RoboticsBrno/semafor/fw/semafor_basic/src/semafor.cpp

#include "Arduino.h"
#include "stateVector.h"
#include "semafor.h"
#include <ctype.h>

#define SECOND 1000
#define MINUTE SECOND*60

String wifi_ssid = "Semafor";
String wifi_password = "adminadmin";
IPAddress wifiIP(192, 168, 1, 1);
IPAddress wifiIPtest(192, 168, 1, 100);
IPAddress netMsk(255, 255, 255, 0);

DNSServer dnsServer;
ESP8266WebServer server(80);

StateVector stateVector;
uint8_t semaforID = 0;

// semafor game config
EEPROM_data stateVector_eeprom(&stateVector, sizeof(stateVector));

// semafor ID
EEPROM_data semaforID_eeprom(&semaforID, sizeof(semaforID));

// UDP server for sharing settings between semafors
WiFiUDP udpSett;
uint8_t udpCheckKey;

uint8_t prevMode = 0;
uint8_t DNS_PORT = 53;


// bool activeLed = false;

void setLed(uint8_t ledID, bool on) {
    if(stateVector.activeLed) {
        analogWrite(ledPins[ledID], on*stateVector.ledBrightness[0]*4);
    }
}
void setLeds(bool red, bool green, bool blue) {
    setLed(0, red);
    setLed(1, green);
    setLed(2, blue);
}
void setLedsAll(bool state) {
    setLed(0, state);
    setLed(1, state);
    setLed(2, state);
}

bool buttonPressed(uint16_t timeMs, bool activeEnd = 1) {
    static uint32_t lastPressed = 0;

    if(activeEnd) {
        if(digitalRead(button)) {
            // not pressed
            lastPressed = 0;
        }
        else if(lastPressed == 0) {
            // firstly pressed
            lastPressed = millis();
        }
        else if(millis() > (lastPressed + timeMs)) {
            // still pressed after time period
            lastPressed = 0;
            return true;
        }
    }
    else {
        if(!digitalRead(button) && millis() > (lastPressed + timeMs)) {
            lastPressed = millis();
            return true;
        }
    }

    return false;
}

void printInfo(semState state) {
    Serial.printf("semaforID: %d\n", semaforID);
    Serial.printf("semafor state: %d\n", state);
    Serial.printf("gameMode: %d\n", stateVector.gameMode);
    Serial.printf("monopolyDelayMin: %d\n", stateVector.monopolyDelayMin);
    Serial.printf("monopolyDelayMax: %d\n", stateVector.monopolyDelayMax);
    Serial.printf("tdPressShort: %d\n", stateVector.tdPressShort);
    Serial.printf("tdPressLong: %d\n", stateVector.tdPressLong);
    Serial.printf("\n");
}

void initLeds() {
    stateVector.activeLed = true;
    for(uint8_t i = 0; i < 3; ++i) {
        pinMode(ledPins[i], OUTPUT);
    }
}

void initSerial() {
    stateVector.activeLed = false;
    Serial.begin(115200);
    for(uint8_t i = 0; i < 3; ++i) {
        pinMode(ledPins[i], SPECIAL);
    }
}


void semaforInit() {
    stateVector_eeprom.read();
    semaforID_eeprom.read();

    initLeds();
    // initSerial();


    pinMode(button, INPUT_PULLUP);

    randomSeed(analogRead(A0));

    delay(500);

    for(int i = 0; i< 3; i++) {
        setLed(i, true);
        delay(200);
    }

    for(int i = 2; i>=0; i--) {
        setLed(i, false);
        delay(200);
    }
}

void settBrodcast() {
    static bool initBrodcast = true;
    static bool blinkCenter = true;
    static ArduinoMetronome blinker(800);
    static ArduinoMetronome sender(500);

    if(initBrodcast) {
        setLeds(true, false, true);

        Serial.println("Start WiFi");
        softApEnable();

        // server routes
        server.on("/", handleRoot);
        server.on("/admin", handleAdmin);
        server.on("/adminsave", handleAdminSave);
        server.on("/datasave", handleDataSave);
        server.on("/addparam", handleAddParam);
            // put "IP/addparam?id=X" into URL for setting semafor ID
            // put "IP/addparam?led=1/0" enable LED / enable Serial
        server.onNotFound(handleRoot);
        server.on("/style.css", handleStyle);
        server.begin();


        // UDP server for sharing settings between semafors
        udpSett.begin(1111);
        initBrodcast = false;
    }

    if(blinker.loopMs()) {
        if(blinkCenter) {
            setLeds(false, true, false);
        }
        else {
            setLeds(true, false, true);
        }
        blinkCenter = !blinkCenter;
    }

    if(sender.loopMs()) {
        Serial.println("Clients coutn: " + String(wifi_softap_get_station_num()));
        struct station_info *station_list = wifi_softap_get_station_info();
        while (station_list != NULL) {
            IPAddress station_ip = ((&station_list->ip)->addr);

            // Serial.println(station_ip.toString());
            udpSett.beginPacket(station_ip, 1111);
            stateVector.transmittCheckNum = semaforID;
            udpSett.write((const uint8_t *) &stateVector, sizeof(stateVector));
            udpSett.endPacket();

            station_list = STAILQ_NEXT(station_list, next);
        }
        wifi_softap_free_station_info();
    }
}

bool settReceive() {
    static bool initReceive = true;
    static bool initConnected = true;
    static bool connected = false;

    static ArduinoMetronome sender(800);

    if(initReceive) {
        wifiEnableConnect();
        initReceive = false;
    }

    if(initConnected && WiFi.status() == WL_CONNECTED) {
        initConnected = false;
        connected = true;
        udpSett.begin(1111);
        Serial.println("Connected to WiFi");
    }

    if(connected) {
        StateVector receiveVector;

        int packetSize = udpSett.parsePacket();
        if (packetSize) {
            int len = udpSett.read((char *) &receiveVector, sizeof(receiveVector));
            if(len>0) {
                stateVector = receiveVector;
                stateVector_eeprom.write();
                Serial.printf("New settings recieved and updated from Semafor ID: %d", receiveVector.transmittCheckNum);

                // success upload blink
                for(int i = 0; i < 6; i++) {
                    setLeds(false, true, true);
                    delay(80);
                    setLeds(true, true, false);
                    delay(80);
                }
                setLeds(false, false, false);
                wifiDisable();

                return true; // jump to Normal mode
            }
            else {
                Serial.printf("Error receive new settings from Semafor ID: %d", receiveVector.transmittCheckNum);
            }
        }
    }

    return false;



}


semState semaforState() {

    semState nowState = S_RECEIVE;

    static bool pressedOnStart = false;
    static int startPressedTime;
    static int startTime = millis();
    int nowTime = millis();

    if(nowTime-startTime < 2 * MINUTE) {
        bool buttonState = !digitalRead(button);

        if(!buttonState) {
            pressedOnStart = false;
            nowState = S_RECEIVE; // if not pressed + until specific time
        }
        else if(buttonState && pressedOnStart == false) { // first press
            startPressedTime = millis();
            pressedOnStart = true;
            nowState = S_RECEIVE;
        }
        else if(pressedOnStart && nowTime-startPressedTime > 3 * SECOND) {
            nowState = S_BRODCAST; //if pressed for 3 sec + until specific time
        }
    }
    else {
        nowState = S_NORMAL; // else
        WiFi.disconnect(true);
    }

    return nowState;
}


void semaforLoop() {
    switch(stateVector.gameMode) {
        case 0:
            handleMonopoly();
            break;
        case 1:
            handleVabicka();
            break;
        case 2:
            handleVlajky();
            break;
        case 3:
            handleTowerDefence();
            break;
        case 4:
            handleHoldToGet();
            break;
        case 5:
            handleMinutka();
            break;
        case 6:
            handleMikrovlnka();
            break;
        default:
            stateVector.gameMode = 0;
    }
    prevMode = stateVector.gameMode;
}


void handleMonopoly() {
    static uint32_t changeDelay = 0;
    static uint32_t lastChange = 0;
    static bool lightStateRG = 1; //0-red, 1-green
    if(stateVector.gameMode != prevMode) {
        lightStateRG = 0;
        lastChange = millis();
    }
    if(millis() > (lastChange + changeDelay)) {
        lastChange = millis();
        changeDelay = 1000 * random(stateVector.monopolyDelayMin, stateVector.monopolyDelayMax);

        lightStateRG = !lightStateRG;
    }
    setLeds(!lightStateRG, lightStateRG, 0);
}
void handleVabicka() {
    static int8_t lightState = 0;  //0-R, 1-G, 2-B, 3-nothing
    if(stateVector.gameMode != prevMode)
        lightState = 0;
    if(buttonPressed(debounce, 0)) {
        ++lightState;
        if(lightState > 2)
            lightState = 0;
    }
    for(uint8_t i = 0; i < 3; ++i) {
        setLed(i, i == lightState);
    }
}
void handleVlajky() {
    static int8_t lightState = 0;  //0-R, 1-G, 2-B, 3-nothing
    if(stateVector.gameMode != prevMode)
        lightState = 0;
    if(buttonPressed(debounce, 0)) {
        ++lightState;
        if(lightState > 3)
            lightState = 0;
    }
    for(uint8_t i = 0; i < 3; ++i) {
        setLed(i, i == lightState);
    }
}
void handleTowerDefence() {
    static uint32_t lastPress = 0;
    static int8_t lightState = 0;  //0-R, 1-G, 2-B, 3-nothing
    static uint8_t buildState = 0; //0-building, 1-short flashing, 2-destroying, 3-flashing
    static bool prevButtonState = 0, buttonState = 0;
    static uint32_t buttonPressedSince = 0;
    if(stateVector.gameMode != prevMode) {
        buildState = 0;
        lightState = 0;
    }
    switch(buildState) {
        case 0:     //building
            buttonState = digitalRead(button);
            if((buttonState && !prevButtonState) && millis() > (lastPress + debounce)) {
                lastPress = millis();
                ++lightState;   //0-nothing, 1-R, 2-RG, 3-RGB
                if(lightState > 3)
                    lightState = 3;
            }
            prevButtonState = buttonState;
            break;
        case 1:     //short flashing
            static uint32_t flashStart = 0;
            static uint8_t flashesCount = 0;
            static int8_t tempLightState;
            if(flashesCount == 0)
                tempLightState = lightState;
            if(millis() > (flashStart + flashPeriod)) {
                flashStart = millis();
                ++flashesCount;
                if(lightState)
                    lightState = 0;
                else
                    lightState = 3;

                if(flashesCount > 20) {
                    flashesCount = 0;
                    flashStart = 0;
                    buildState = 2;
                    lightState = tempLightState;
                }
            }
            break;
        case 2:     //destroying
            static uint32_t buttonPressedSinceShort = 0;
            if(!digitalRead(button)) {
                if(buttonPressedSinceShort == 0)
                    buttonPressedSinceShort = millis();
                if(millis() > buttonPressedSinceShort + 1000*stateVector.tdPressShort) {
                    buttonPressedSinceShort = millis();
                    --lightState;
                    if(lightState <= 0) {
                        lightState = 0;
                        buildState = 3;
                    }
                }
            }
            else {
                buttonPressedSinceShort = 0;
            }
            break;
        default:    //case 3 - flashing
            if(millis() > (flashStart + flashPeriod)) {
                flashStart = millis();
                if(lightState)
                    lightState = 0;
                else
                    lightState = 3;
            }
            break;
    }

    if(!digitalRead(button)) {
        if(buttonPressedSince == 0)
            buttonPressedSince = millis();
        if(millis() > buttonPressedSince + 1000*stateVector.tdPressLong) {
            buttonPressedSince = millis();
            if(buildState == 0) {
                buildState = 1;
            }
            else {
                buildState = 0;
                lightState = -1;
            }
        }
    }
    else {
        buttonPressedSince = 0;
    }

    for(uint8_t i = 0; i < 3; ++i) {
        setLed(ledPins[i], i < lightState);
    }
    //Serial.printf("%d   %d\n", buildState, lightState);
}

void handleHoldToGet() {
    ;
    // static ArduinoMetronome blinker(500, 4);
    // static uint8_t state = 0;

    // if(blinker.counterLoop()) {
    //     if(blinker.loopMs()) {
    //         if(blinker.counterNowGet()%2) {
    //             setLedsAll(0);
    //         }
    //         else {
    //             setLedsAll(1);
    //         }


    //         blinker.counterNowIncrease();
    //     }
    // } else {
    //     setLeds(1,0,1);
    //     Serial.println("END");
    // }
}

void handleMinutka() {
    static uint8_t state = 0;
    static uint16_t timeStart;
    uint16_t timeNow = millis()/1000;
    uint16_t thirdOfTime = stateVector.minutkaTimeSecAll/3;

    switch (state)
    {
    case 0: // wait on start, leds off
        if(!digitalRead(button)) {
            state = 1;
        }
        break;
    case 1: // all leds on
        setLeds(true, true, true);
        state = 2;
        timeStart = millis()/1000;
        break;
    case 2:
        if(timeNow-timeStart > thirdOfTime) {
            setLeds(true, true, false);
            state = 3;
        }
        break;
    case 3:
        if(timeNow-timeStart > thirdOfTime*2) {
            setLeds(true, false, false);
            state = 4;
        }
        break;
    case 4:
        if(timeNow-timeStart > (stateVector.minutkaTimeSecAll - 10)) {
            state = 5;
        }
        break;

    case 5: // blink 10 seconds before end
        static bool blinkCenter = true;
        static ArduinoMetronome blinker(800);

        if(timeNow-timeStart > stateVector.minutkaTimeSecAll) {
            setLedsAll(false);
            state = 6;
        }

        if(blinker.loopMs()) {
            if(blinkCenter) {
                setLedsAll(true);
            }
            else {
                setLedsAll(false);
            }
            blinkCenter = !blinkCenter;
        }
        break;

    case 6:
        state = 0;
        break;
    }
}


void handleMikrovlnka() {
    static uint8_t state = 0;
    static uint16_t timeStart;
    uint16_t timeNow = millis()/1000;
    uint16_t thirdOfTime = stateVector.minutkaTimeSecAll/3;

    switch (state)
    {
    case 0: // all leds light before start
        setLedsAll(true);
        state = 1;

    case 1: // wait on start
        if(!digitalRead(button)) {
            setLedsAll(false);
            timeStart = millis()/1000;
            state = 2;
        }
        break;
    case 2:
        if(timeNow-timeStart > thirdOfTime) {
            setLeds(false, false, true);
            state = 3;
        }
        break;
    case 3:
        if(timeNow-timeStart > thirdOfTime*2) {
            setLeds(false, true, true);
            state = 4;
        }
        break;
    case 4:
        if(timeNow-timeStart > (stateVector.minutkaTimeSecAll - 10)) {
            state = 5;
        }
        break;

    case 5: // blink 10 seconds before end
        static bool blinkCenter = true;
        static ArduinoMetronome blinker(800);

        if(timeNow-timeStart > stateVector.minutkaTimeSecAll) {
            setLedsAll(true);
            state = 6;
        }

        if(blinker.loopMs()) {
            if(blinkCenter) {
                setLedsAll(true);
            }
            else {
                setLedsAll(false);
            }
            blinkCenter = !blinkCenter;
        }
        break;

    case 6:
        break;
    }
}
