RoboticsBrno/semafor/fw/semafor_riddle/src/handleHttp.h

#ifndef _HANDLE_HTTP_
#define _HANDLE_HTTP_

/** Handle root or redirect to captive portal */
void handlaDataSave();
void handleRoot();
void handleTask2();
void handleTask3();
void handleResult();
void softApEnable();
void softApDisable();

#endif
